psychogenic/spasics/python/transaction_generator.py

'''
@author: Pat Deegan
@copyright: Copyright (C) 2025 Pat Deegan, https://psychogenic.com

Simple system to convert experiment command schedules (@see doc/ExperimentRequests.ods) to 
a CSV for transmission from ground station to sat.

Steps:
  * fill in ExperimentRequests.ods by setting datetime/deltas for individual commands
  * export that to a CSV
  * use this module to 
     generator = generate('/path/to/reqs.csv')
     # and then
     generator.writeCSV('/path/to/schedule_bytes.csv')
     

'''

from i2c_client_test import packetdump
import csv 
import datetime

UseWindowRelativeTimes = True

DeviceBusIdDefault = 0x56

VerboseOutput = False

class TSPacket:
    def __init__(self, action, ts, packets=None):
        self.action = action
        self.timestamp = ts 
        self.packets = packets 
        
    def __repr__(self):
        return f'<TSPacket {self.action} {self.timestamp}: {self.packets}>'
    
class CSVGenerator:
    
    def __init__(self, device_bus_id:int=DeviceBusIdDefault):
        self.tspackets = [] 
        self.current_pack = None 
        self.include_bytes_column = False
        self.hexpack_little_endian = False
        packetdump.extend_packets = True
        self.bus_id = device_bus_id
        
        
        
    def append(self, row, ts):
        
        if self.current_pack is None:
            self.current_pack = TSPacket(row['action'], ts)
        else:
            if ts == self.current_pack.timestamp:
                self.current_pack.action += f" {row['action']}"
            else:
                self.flush()
                self.current_pack = TSPacket(row['action'], ts)
        
        
    def flush(self):
        if self.current_pack is not None:
            self.current_pack.packets = packetdump.packets()
            
            if len(self.current_pack.packets):
                while len(self.current_pack.packets[-1]) < 8:
                    self.current_pack.packets[-1] += bytearray([0])
                    
            self.tspackets.append(self.current_pack)
        self.current_pack = None
            
    def abort(self, timestamp, row):
        self.append(row, timestamp)
        packetdump.abort()
    def run(self, timestamp, row):
        (expid, args) = self.get_experiment_and_parms(row)
        print(f"Run exp {expid} w args {args}")
        self.append(row, timestamp)
        packetdump.run_experiment_now(expid, args)
                
    def reboot(self, timestamp, row):
        self.append(row, timestamp)
        packetdump.reboot()
        
    def status(self, timestamp, row):
        self.append(row, timestamp)
        packetdump.status()
        
    def result(self, timestamp, row):
        self.append(row, timestamp)
        packetdump.experiment_current_results()
        
    def ping(self, timestamp, row):
        self.append(row, timestamp)
        cnt = self.get_parms(row)
        if cnt:
            if len(cnt) > 1:
                packetdump.ping(cnt[0], cnt[1:])
            else:
                packetdump.ping(cnt[0])
                
        else:
            packetdump.ping()
        
        
    def info(self, timestamp, row):
        self.append(row, timestamp)
        packetdump.info()
        
    def queue(self, timestamp, row):
        (expid, args) = self.get_experiment_and_parms(row)
        self.append(row, timestamp)
        packetdump.experiment_queue(expid, args)
        
    def writeCSV(self, topath:str):
        # format_code = "%Y-%m-%d %H:%M:%S"
        # official format is :
        # event_id,deadline,1 byte address,8 byte data
        # with:
        #  - event_id: I2C_EXPS_EVENT_SEND_COMMAND
        #  - deadline: 0==immediate,  
        #               <0 -> scheduled execution, ABS(deadline) second later  
        #               >0 -> scheduled execution, deadline must be a POSIX timestamp
        
        event_id = 'I2C_EXPS_EVENT_SEND_COMMAND'
        bus_address = hex(self.bus_id)
        self.bus_id
        with open(topath, "w") as f:
            writer = csv.writer(f, delimiter=',',
                            quotechar='"', quoting=csv.QUOTE_MINIMAL)
            if self.hexpack_little_endian:
                hexheader = 'write (hex, little-end)'
            else:
                hexheader = 'write (hex, big-end)'
            header = ['#evend_id', 'deadline', 'address', hexheader]
            writer.writerow(header)
            
            firstDatetime = None 
            lastDatetime = None 
            for tspack in self.tspackets:
                writepacks = ''
                hexpacks = ''
                
                curDateTime = tspack.timestamp # datetime.datetime.strptime(, format_code)
                delta_s = 0
                if firstDatetime is None:
                    firstDatetime = curDateTime
                else:
                    if UseWindowRelativeTimes:
                        delta_s = tspack.timestamp
                    else:
                        deltaT = curDateTime - firstDatetime
                        delta_s = deltaT.total_seconds()
                
                lastDatetime = curDateTime
                
                txpacket_count = 0
                for p in tspack.packets:
                    if type(p) == bytearray:
                        if self.hexpack_little_endian:
                            p = bytearray(list(reversed(p)))
                        hexpacks = f'0x{p.hex()}'
                    writepacks = p
                    if txpacket_count:
                        action = f'{tspack.action} (cont)'
                    else:
                        action = tspack.action
                    
                    if UseWindowRelativeTimes:
                        deadline = f'{int(delta_s)}' if delta_s else '0'
                    else:
                        deadline = f'-{int(delta_s)}' if delta_s else '0'
                    
                    if self.include_bytes_column:
                        row = [tspack.timestamp, action, writepacks, hexpacks, delta_s]
                    else:
                        row = [event_id, deadline, bus_address, hexpacks]
                    
                    writer.writerow(row)
                    
                    txpacket_count += 1

    def get_parms(self, row):
        bts = ''
        if len(row['param']):
            prm = row['param']
            if prm[0] == 'b' and prm[1] == "'":
                bts = eval(prm)
            elif prm[0] == '0' and prm[1] == 'x':
                try:
                    bts = bytearray.fromhex(prm[2:])
                except Exception as e:
                    print(e)
                    print(f'Problem in {prm[2:]}')
                    raise e
            else:
                print(f"INVALID PARAM {prm}")
                
        return bts

    def get_experiment_and_parms(self, row):
        expid = None
        if len(row['experiment id']):
            try:
                expid = int(row['experiment id'])
                if VerboseOutput:
                    print(f"EXPID {expid}")
            except:
                print(f"Invalid experiment {row['experiment id']}")
        bts = self.get_parms(row)
        return (expid, bts)
def generate(csvfile:str) -> CSVGenerator:
    #expects start datetime,    delta ms,    action,    experiment,    param,    experiment id, comment, packet datetime
    # with action being one of:
    # Run
    # Abort
    # Reboot
    # Status
    # Result
    # Ping
    # Info
    # Queue
    
    generator = CSVGenerator()
    with open(csvfile) as f:
        reader = csv.DictReader(f, delimiter=',', quotechar='"')
        
        lastread = None
        rowCount = 0
        seconds_counter = 0
        for row in reader:
            # print(f"ROW {row}")
            if UseWindowRelativeTimes:
                if not len(row['delta s']) and rowCount:
                    continue
            else:
                if not len(row['packet datetime']):
                    continue 
            if not len(row['action']):
                continue 
            
            
            rowCount += 1
            if VerboseOutput:
                print(f'Line {rowCount}: {row}')
            
            # print(row)
            
            action = row['action'].lower()
            
            if not hasattr(generator, action):
                print(f"Unsupported action {action}")
                continue
                
            
            needFlush = False
            if UseWindowRelativeTimes:
                cur_delay = int(row['delta s']) if len(row['delta s']) else 0
                dt = -1 * (seconds_counter + cur_delay)
                seconds_counter += cur_delay
                if lastread is None or cur_delay > 9:
                    needFlush = True
            else:
                dt = datetime.datetime.fromisoformat(row['packet datetime'])
                if lastread is None or (dt - lastread) > datetime.timedelta(seconds = 9):
                    needFlush = True 
            print(f"Calling ACTION {action} @ {dt}")
            act = getattr(generator, action)
            act(dt, row)
            
            if lastread is None or needFlush:
                generator.flush()
                lastread = dt
        
        generator.flush()
                
    return generator


import argparse 
def getArgs():
    global VerboseOutput
    parser = argparse.ArgumentParser(
        description="Telemetry parser"
    )
    
    parser.add_argument(
        'inputfile', 
        type=str,
        help='The path to the input CSV to process'
    )
    
    
    parser.add_argument(
        'outputfile', 
        type=str,
        help='The path to the output CSV to generate for BME'
    )
    parser.add_argument('--verbose', action=argparse.BooleanOptionalAction, 
        default=False)
    
    args =  parser.parse_args()
    if args.verbose:
        VerboseOutput = True
        
    return args

if __name__ == '__main__':
    args = getArgs()
    if args.inputfile == args.outputfile:
        print("input should NOT be the same as output")
    else:
        gen = generate(args.inputfile)
        print(f'Read in {args.inputfile}, writing {args.outputfile}')
        gen.writeCSV(args.outputfile)
        
