psychogenic/spasics/python/i2c_server_globals.py

import time
from spasic.fs.filesystem import FSAccess
from spasic.variables.variables import Variables
from spasic.experiment.experiment_result import ExpResult
from spasic.experiment.experiment_parameters import ExperimentParameters
from ttboard.demoboard import DemoBoard

FileSystem = FSAccess()
ERes = ExpResult()
ExpArgs = ExperimentParameters(DemoBoard.get())
ClientVariables = Variables()
PendingDataIn = [bytearray(9), bytearray(9), bytearray(9), bytearray(9), bytearray(9), bytearray(9)]
PendingDataNum = 0
PendingDataOut = []
ExperimentQueue = []
ExperimentRun = False
LastTimeSyncMessageTime = -1
LastTimeSyncValue = 0
LastAutoMessageTime = 0

def sync_time_now(t_now:int=None):
    if t_now is None:
        t_now = int(time.time())
        
    if LastTimeSyncMessageTime > 0:
        t_sync = LastTimeSyncValue + (t_now - LastTimeSyncMessageTime)
    else:
        t_sync = 0xefbeadde
    return t_sync
