psychogenic/spasics/python/spasic/experiment/tt_um_PAL/loader.py

# SPDX-License-Identifier: Apache2.0
# Copyright (C) 2025 Ken Pettit

from spasic.experiment.experiment_result import ExpResult
from spasic.experiment.experiment_parameters import ExperimentParameters
import sys
def run_experiment(params: ExperimentParameters, response: ExpResult):
    try:
        import spasic.experiment.tt_um_PAL.be_a_PAL
        spasic.experiment.tt_um_PAL.be_a_PAL.exercise(params, response)
    
    except Exception as e:
        response.exception = e
        sys.print_exception(e) # DEBUG
    else:
        response.completed = True
    return
