psychogenic/spasics/python/spasic/experiment/rp2_temperature/loader.py

'''
Created on Apr 30, 2025

@author: Pat Deegan
@copyright: Copyright (C) 2025 Pat Deegan, https://psychogenic.com
'''

from spasic.experiment.experiment_result import ExpResult
from spasic.experiment.experiment_parameters import ExperimentParameters

def run_experiment(params:ExperimentParameters, response:ExpResult):
    
    # always wrap everything in a try block
    try:
        # import HERE, inside the function, 
        # such that loading all the experiment runners doesn't 
        # eat a ton of memory by pre-importing everything
        import spasic.experiment.rp2_temperature.temperature
        
        # run that experiment
        spasic.experiment.rp2_temperature.temperature.test_temperature(params, response)
        
    except Exception as e:
        # an exception occurred... 
        # let the server know about it
        response.exception = e 
    else:
        # we get here, all went well
        # mark the experiment as completed
        response.completed = True
    return
